vincentlaurens/5ISS_Save_Water_and_Energy/Minimization/PCB/Other_version_of_PCB/KicadILYA_former_without_groundPlan/imagePCB/FrontRoutage.png

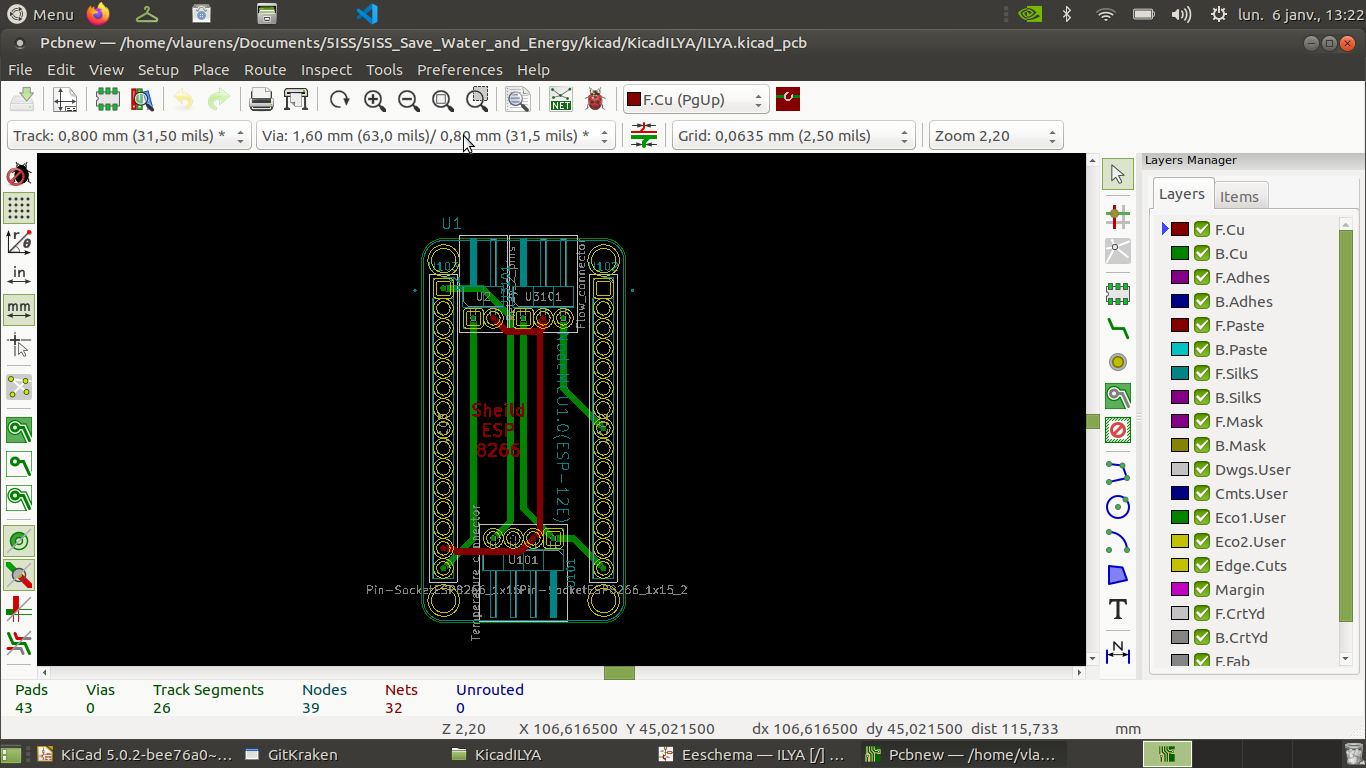
Minimization/PCB/Other_version_of_PCB/KicadILYA_former_without_groundPlan/imagePCB/FrontRoutage.png
