vincentlaurens/5ISS_Save_Water_and_Energy/Minimization/PCB/Other_version_of_PCB/KicadILYAWemos/BoadShieldEmpty.png

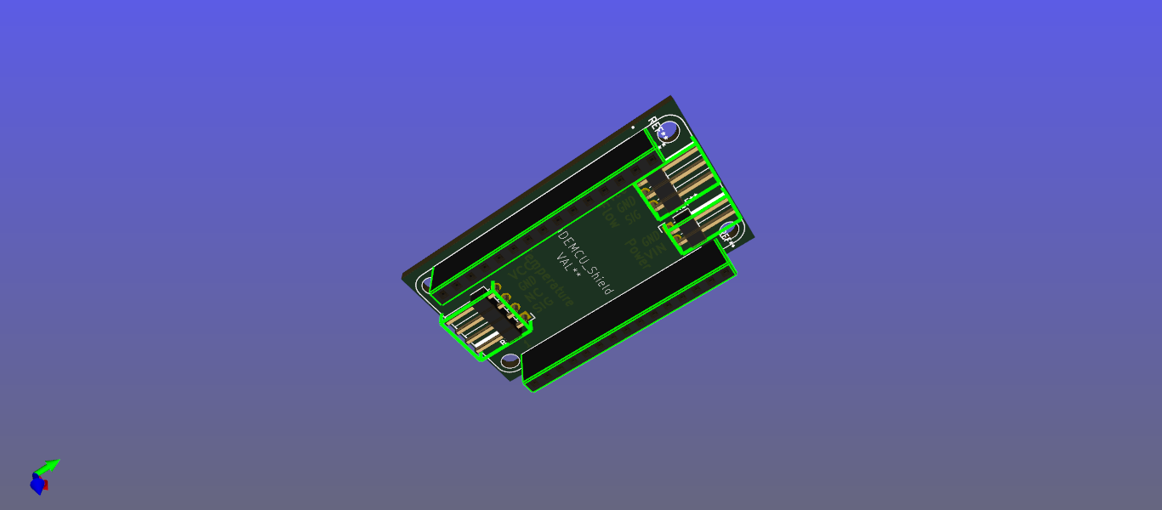
Minimization/PCB/Other_version_of_PCB/KicadILYAWemos/BoadShieldEmpty.png
