vincentlaurens/5ISS_Save_Water_and_Energy/Minimization/PCB/Other_version_of_PCB/KicadILYAWemos/ILYA_FULL_BACK.png

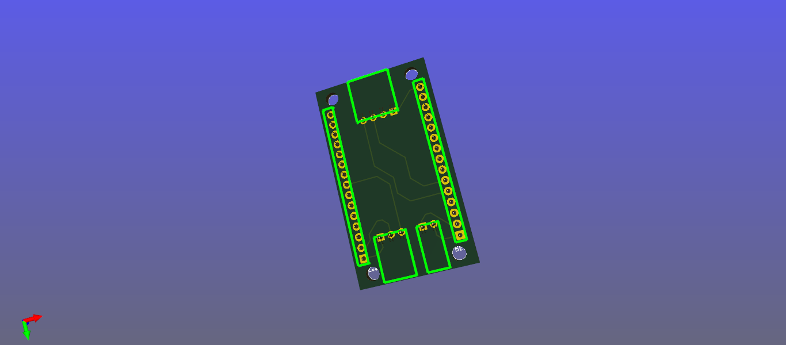
Minimization/PCB/Other_version_of_PCB/KicadILYAWemos/ILYA_FULL_BACK.png
